lyuboasenov/MxA/docs/imgs/IMG_20230511_182956.jpg

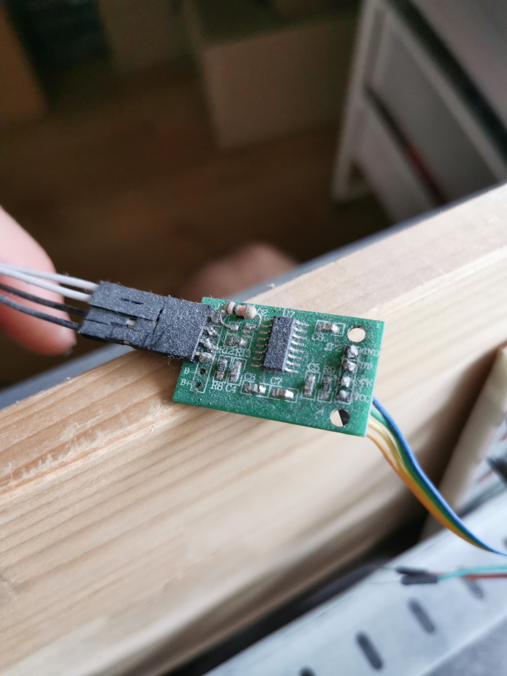
docs/imgs/IMG_20230511_182956.jpg
