lyuboasenov/MxA/docs/imgs/IMG_20230614_184959.jpg

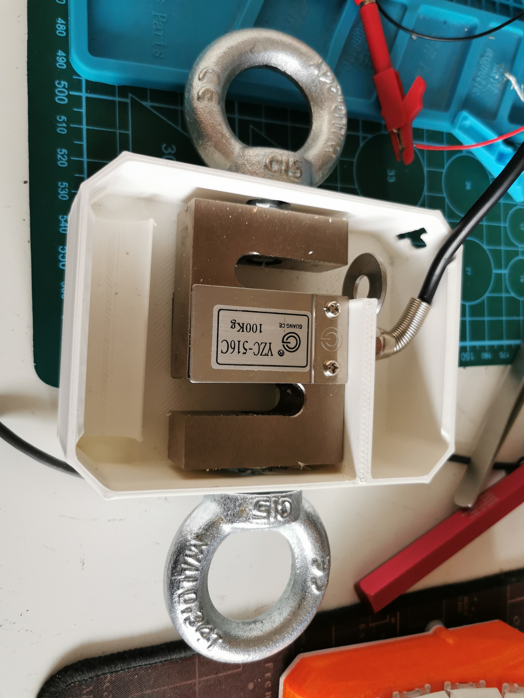
docs/imgs/IMG_20230614_184959.jpg
