lyuboasenov/MxA/docs/imgs/IMG_20230614_185005.jpg

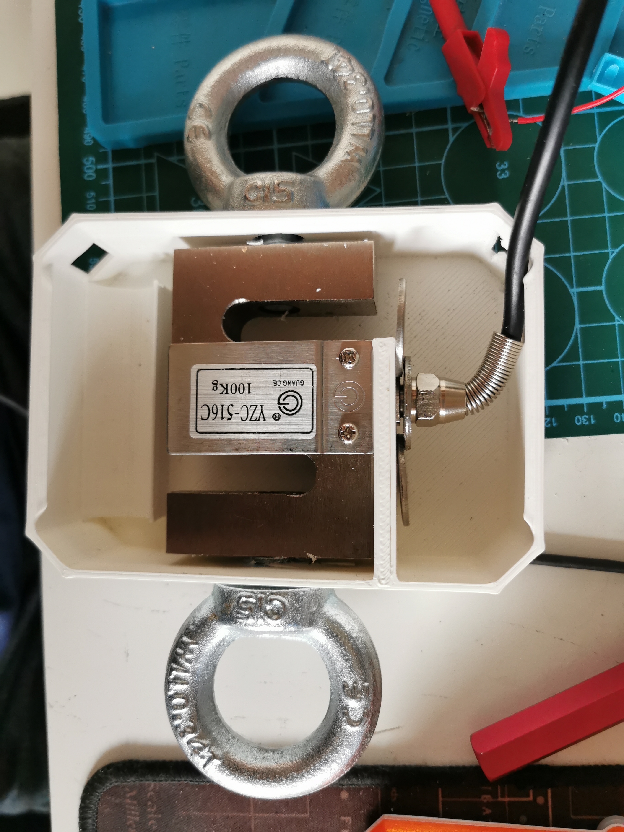
docs/imgs/IMG_20230614_185005.jpg
