lyuboasenov/MxA/docs/imgs/IMG_20230614_185014.jpg

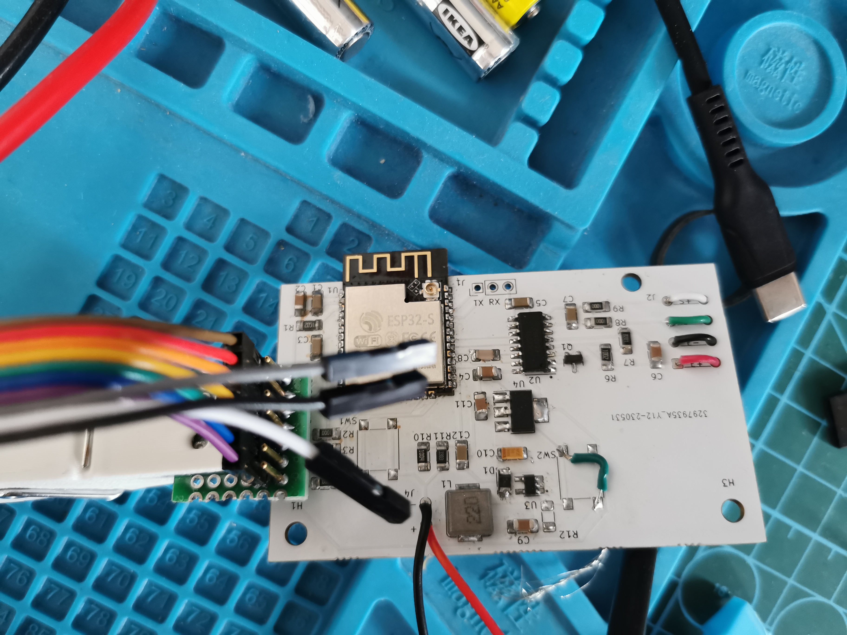
docs/imgs/IMG_20230614_185014.jpg
