lyuboasenov/MxA/docs/imgs/IMG_20230616_191653.jpg

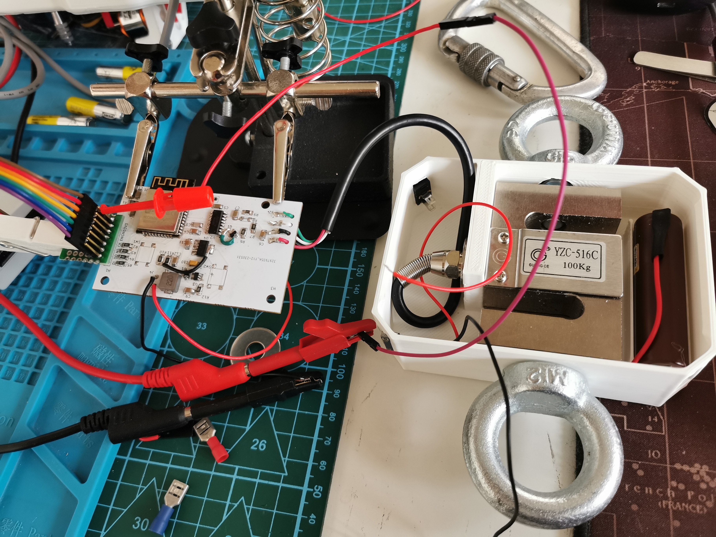
docs/imgs/IMG_20230616_191653.jpg
