lyuboasenov/MxA/docs/imgs/IMG_20230702_162838.jpg

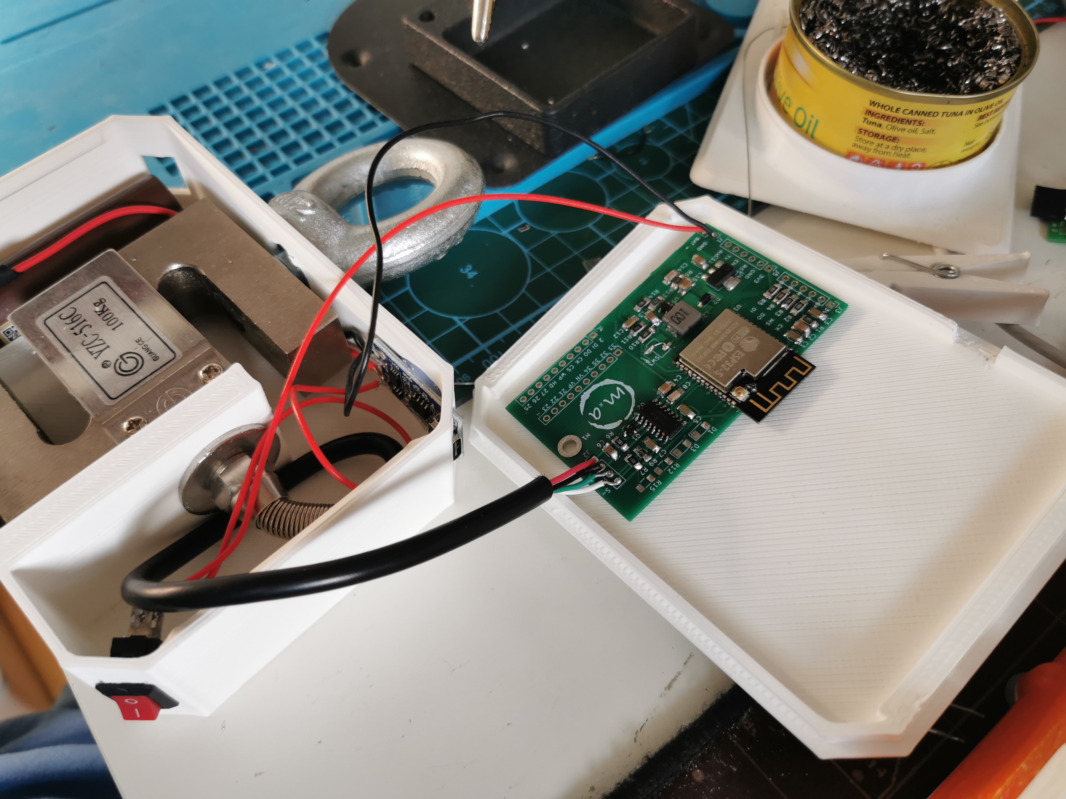
docs/imgs/IMG_20230702_162838.jpg
